DesignedbyAmpersand/Null-Nano/Eagle/PCB Back.png

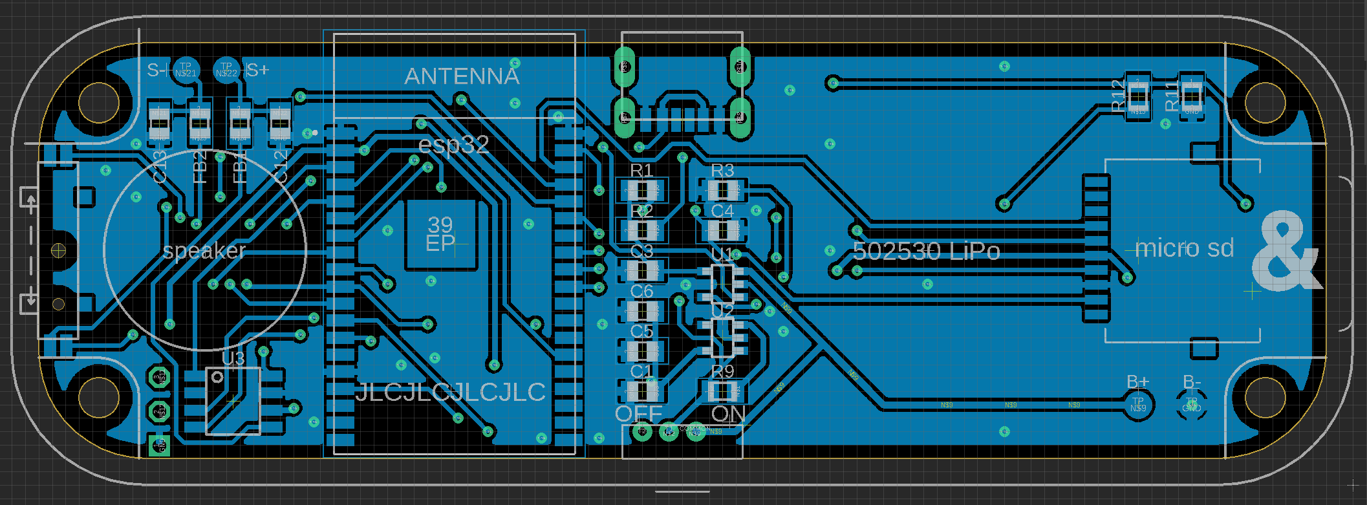
Eagle/PCB Back.png
