DesignedbyAmpersand/Null-Nano/Eagle/PCB Front.png

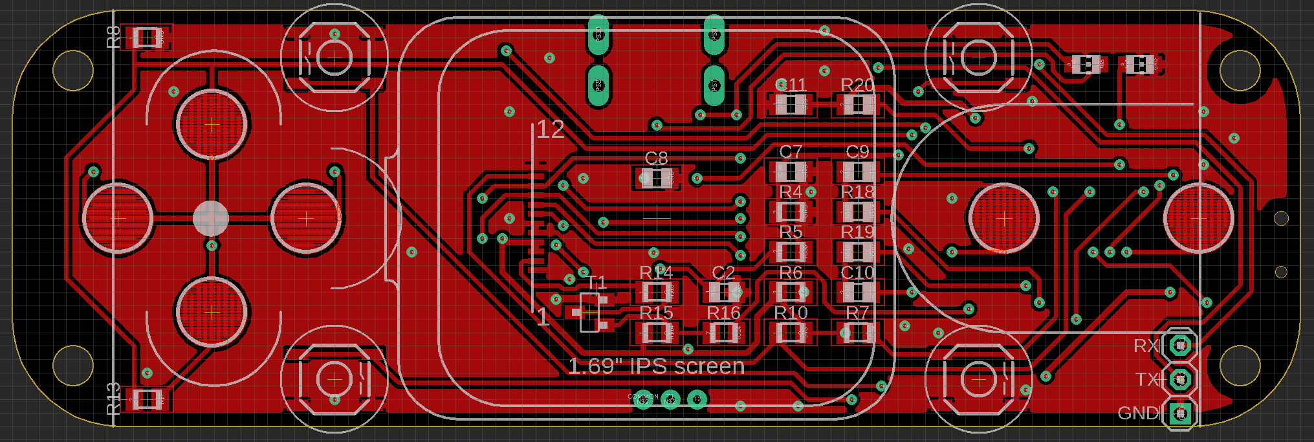
Eagle/PCB Front.png
