DesignedbyAmpersand/Null-Nano/Gradient Goop/background_2600.png

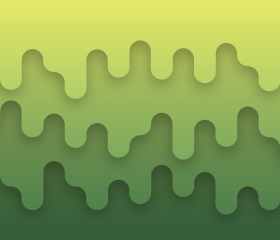
Gradient Goop/background_2600.png
