DesignedbyAmpersand/Null-Nano/Gradient Goop/background_col.png

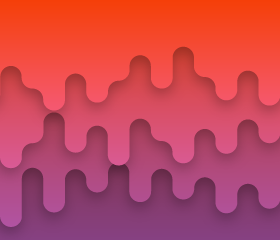
Gradient Goop/background_col.png
