DesignedbyAmpersand/Null-Nano/Gradient Goop/background_doom.png

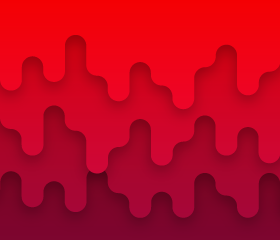
Gradient Goop/background_doom.png
