DesignedbyAmpersand/Null-Nano/Gradient Goop/background_favorite.png

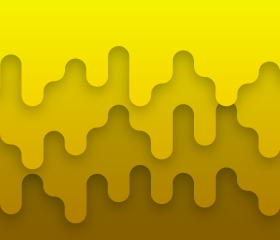
Gradient Goop/background_favorite.png
