DesignedbyAmpersand/Null-Nano/Gradient Goop/background_gb.png

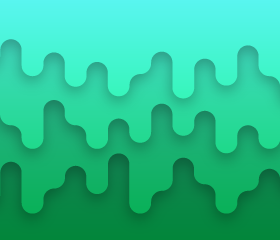
Gradient Goop/background_gb.png
