DesignedbyAmpersand/Null-Nano/Gradient Goop/background_gbc.png

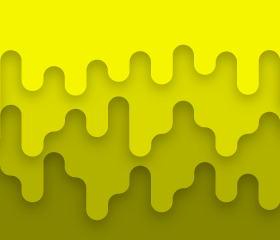
Gradient Goop/background_gbc.png
