DesignedbyAmpersand/Null-Nano/Gradient Goop/background_gg.png

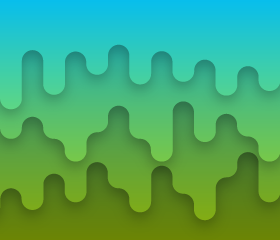
Gradient Goop/background_gg.png
