DesignedbyAmpersand/Null-Nano/Gradient Goop/background_gw.png

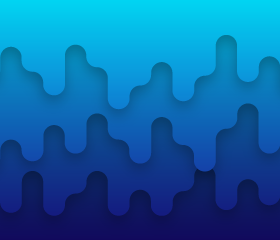
Gradient Goop/background_gw.png
