DesignedbyAmpersand/Null-Nano/Gradient Goop/background_lnx.png

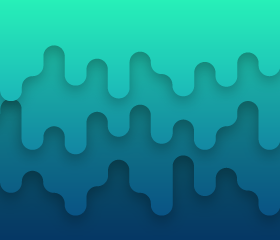
Gradient Goop/background_lnx.png
