DesignedbyAmpersand/Null-Nano/Gradient Goop/background_md.png

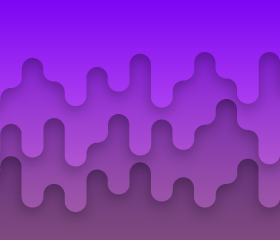
Gradient Goop/background_md.png
