DesignedbyAmpersand/Null-Nano/Gradient Goop/background_nes.png

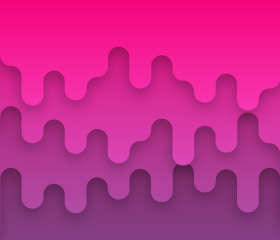
Gradient Goop/background_nes.png
