DesignedbyAmpersand/Null-Nano/Gradient Goop/background_pce.png

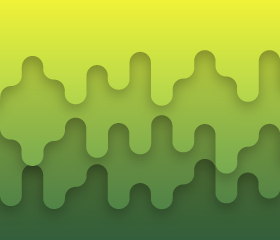
Gradient Goop/background_pce.png
