DesignedbyAmpersand/Null-Nano/Gradient Goop/background_recent.png

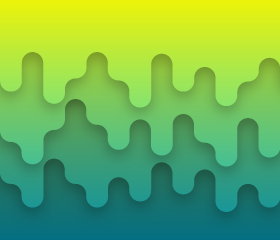
Gradient Goop/background_recent.png
