DesignedbyAmpersand/Null-Nano/Gradient Goop/background_sms.png

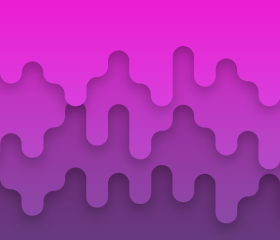
Gradient Goop/background_sms.png
