DesignedbyAmpersand/Null-Nano/Gradient Goop/background_snes.png

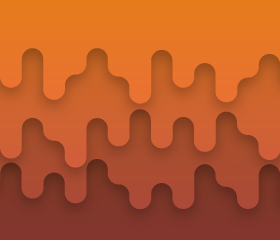
Gradient Goop/background_snes.png
